rdlynx19/paper-byte/code/src/epub/Epub.cpp

#include <sys/types.h>
#include <sys/stat.h>
#include <unistd.h>
#ifndef UNIT_TEST
#include <esp_log.h>
#include <esp_system.h>
#include <freertos/FreeRTOS.h>
#include <freertos/task.h>
#else
#define ESP_LOGI(tag, args...) \
  printf(args);                \
  printf("\n");
#define ESP_LOGE(tag, args...) \
  printf(args);                \
  printf("\n");
#define ESP_LOGD(tag, args...) \
  printf(args);                \
  printf("\n");
#define ESP_LOGW(tag, args...) \
  printf(args);                \
  printf("\n");
#endif
#include <map>
#include "../vendor/tinyxml2.h"
#include "ZipFile.h"
#include "Epub.h"

static const char *TAG = "EPUB";

bool Epub::find_content_opf_file(ZipFile &zip, std::string &content_opf_file)
{
  // open up the meta data to find where the content.opf file lives
  char *meta_info = (char *)zip.read_file_to_memory("META-INF/container.xml");
  if (!meta_info)
  {
    ESP_LOGE(TAG, "Could not find META-INF/container.xml");
    return false;
  }
  // parse the meta data
  tinyxml2::XMLDocument meta_data_doc;
  auto result = meta_data_doc.Parse(meta_info);
  // finished with the data as it's been parsed
  free(meta_info);
  if (result != tinyxml2::XML_SUCCESS)
  {
    ESP_LOGE(TAG, "Could not parse META-INF/container.xml");
    return false;
  }
  auto container = meta_data_doc.FirstChildElement("container");
  if (!container)
  {
    ESP_LOGE(TAG, "Could not find container element in META-INF/container.xml");
    return false;
  }
  auto rootfiles = container->FirstChildElement("rootfiles");
  if (!rootfiles)
  {
    ESP_LOGE(TAG, "Could not find rootfiles element in META-INF/container.xml");
    return false;
  }
  // find the root file that has the media-type="application/oebps-package+xml"
  auto rootfile = rootfiles->FirstChildElement("rootfile");
  while (rootfile)
  {
    const char *media_type = rootfile->Attribute("media-type");
    if (media_type && strcmp(media_type, "application/oebps-package+xml") == 0)
    {
      const char *full_path = rootfile->Attribute("full-path");
      if (full_path)
      {
        content_opf_file = full_path;
        return true;
      }
    }
    rootfile = rootfile->NextSiblingElement("rootfile");
  }
  ESP_LOGE(TAG, "Could not get path to content.opf file");
  return false;
}

bool Epub::parse_content_opf(ZipFile &zip, std::string &content_opf_file)
{
  // read in the content.opf file and parse it
  char *contents = (char *)zip.read_file_to_memory(content_opf_file.c_str());
  // parse the contents
  tinyxml2::XMLDocument doc;
  auto result = doc.Parse(contents);
  free(contents);
  if (result != tinyxml2::XML_SUCCESS)
  {
    ESP_LOGE(TAG, "Error parsing content.opf - %s", doc.ErrorIDToName(result));
    return false;
  }
  auto package = doc.FirstChildElement("package");
  if (!package)
  {
    ESP_LOGE(TAG, "Could not find package element in content.opf");
    return false;
  }
  // get the metadata - title and cover image
  auto metadata = package->FirstChildElement("metadata");
  if (!metadata)
  {
    ESP_LOGE(TAG, "Missing metadata");
    return false;
  }
  auto title = metadata->FirstChildElement("dc:title");
  if (!title)
  {
    ESP_LOGE(TAG, "Missing title");
    return false;
  }
  m_title = title->GetText();

  auto creator = metadata->FirstChildElement("dc:creator");
  if (creator && creator->GetText())
    m_author = creator->GetText();
  else
    ESP_LOGW(TAG, "Missing author");

  auto cover = metadata->FirstChildElement("meta");
  while (cover && cover->Attribute("name") && strcmp(cover->Attribute("name"), "cover") != 0)
  {
    cover = cover->NextSiblingElement("meta");
  }
  if (!cover)
  {
    ESP_LOGW(TAG, "Missing cover");
  }
  auto cover_item = cover ? cover->Attribute("content") : nullptr;
  // read the manifest and spine
  // the manifest gives us the names of the files
  // the spine gives us the order of the files
  // we can then read the files in the order they are in the spine
  auto manifest = package->FirstChildElement("manifest");
  if (!manifest)
  {
    ESP_LOGE(TAG, "Missing manifest");
    return false;
  }
  // create a mapping from id to file name
  auto item = manifest->FirstChildElement("item");
  std::map<std::string, std::string> items;
  // EPUB3 fallback: <item properties="cover-image" .../>, used when there's
  // no EPUB2-style <meta name="cover"> (or its referenced id doesn't match
  // any manifest item).
  std::string epub3_cover_href;

  while (item)
  {
    const char *id_attr   = item->Attribute("id");
    const char *href_attr = item->Attribute("href");
    if (id_attr && href_attr) {
      std::string item_id = id_attr;
      std::string href    = m_base_path + href_attr;
      if (cover_item && item_id == cover_item)
        m_cover_image_item = href;
      if (item_id == "ncx")
        m_toc_ncx_item = href;
      const char *properties = item->Attribute("properties");
      if (properties && std::string(properties).find("cover-image") != std::string::npos)
        epub3_cover_href = href;
      items[item_id] = href;
    }
    item = item->NextSiblingElement("item");
  }
  if (m_cover_image_item.empty())
    m_cover_image_item = epub3_cover_href;
  // find the spine
  auto spine = package->FirstChildElement("spine");
  if (!spine)
  {
    ESP_LOGE(TAG, "Missing spine");
    return false;
  }
  // The spine's own toc="..." attribute is the authoritative reference to
  // the NCX manifest item — its id isn't required to be "ncx" (e.g. some
  // EPUB3 exports use id="toc" instead), so prefer it over the id=="ncx"
  // naming convention checked in the manifest loop above.
  const char *toc_id = spine->Attribute("toc");
  if (toc_id && items.find(toc_id) != items.end())
    m_toc_ncx_item = items[toc_id];
  // read the spine
  auto itemref = spine->FirstChildElement("itemref");
  while (itemref)
  {
    auto id = itemref->Attribute("idref");
    if (items.find(id) != items.end())
    {
      m_spine.push_back(std::make_pair(id, items[id]));
    }
    itemref = itemref->NextSiblingElement("itemref");
  }
  return true;
}

bool Epub::parse_toc_ncx_file(ZipFile &zip)
{
  // the ncx file should have been specified in the content.opf file
  if (m_toc_ncx_item.empty())
  {
    ESP_LOGE(TAG, "No ncx file specified");
    return false;
  }
  ESP_LOGI(TAG, "toc path: %s\n", m_toc_ncx_item.c_str());

  char *ncx_data = (char *)zip.read_file_to_memory(m_toc_ncx_item.c_str());
  if (!ncx_data)
  {
    ESP_LOGE(TAG, "Could not find %s", m_toc_ncx_item.c_str());
    return false;
  }
  // Parse the Toc contents
  tinyxml2::XMLDocument doc;
  auto result = doc.Parse(ncx_data);
  free(ncx_data);
  if (result != tinyxml2::XML_SUCCESS)
  {
    ESP_LOGE(TAG, "Error parsing toc %s", doc.ErrorIDToName(result));
    return false;
  }
  auto ncx = doc.FirstChildElement("ncx");
  if (!ncx)
  {
    ESP_LOGE(TAG, "Could not find first child ncx in toc");
    return false;
  }

  auto navMap = ncx->FirstChildElement("navMap");
  if (!navMap)
  {
    ESP_LOGE(TAG, "Could not find navMap child in ncx");
    return false;
  }

  parse_nav_points(navMap, 0);
  return true;
}

void Epub::parse_nav_points(tinyxml2::XMLElement *parent, int level)
{
  // Defensive cap on recursion depth — a real book's TOC is a handful of
  // levels deep at most; this just guards against a malformed or
  // pathologically nested NCX rather than reflecting any real limit.
  if (level > 8) return;

  auto navPoint = parent->FirstChildElement("navPoint");
  while (navPoint)
  {
    std::string title = "";
    auto navLabelEl = navPoint->FirstChildElement("navLabel");
    if (navLabelEl) {
      auto textEl = navLabelEl->FirstChildElement("text");
      if (textEl) {
        auto textNode = textEl->FirstChild();
        if (textNode) title = textNode->Value();
      }
    }

    auto content = navPoint->FirstChildElement("content");
    if (content) {
      const char *src = content->Attribute("src");
      if (src) {
        std::string href = m_base_path + src;
        std::string anchor = "";
        size_t pos = href.find('#');
        if (pos != std::string::npos) {
          anchor = href.substr(pos + 1);
          href   = href.substr(0, pos);
        }
        m_toc.push_back(EpubTocEntry(title, href, anchor, level));
      }
    }

    // Recurse before moving to the next sibling, so a parent's entry is
    // always immediately followed by all of its own descendants in m_toc
    // (depth-first, document order) before the next top-level entry.
    parse_nav_points(navPoint, level + 1);
    navPoint = navPoint->NextSiblingElement("navPoint");
  }
}

Epub::Epub(const std::string &path) : m_path(path)
{
}

// load in the meta data for the epub file
bool Epub::load()
{
  ZipFile zip(m_path.c_str());
  std::string content_opf_file;
  if (!find_content_opf_file(zip, content_opf_file))
  {
    #ifndef UNIT_TEST
      #ifdef USE_SPIFFS
        ESP_LOGI(TAG, "Is SPIFFs data uploaded?\npio run -t uploadfs");
      #endif
      ESP_LOGE(TAG, "Could not open ePub. Restarting in 10 secs.");
      vTaskDelay(pdMS_TO_TICKS(1000*10));
      esp_restart();
    #endif
    return false;
  }
  // get the base path for the content
  m_base_path = content_opf_file.substr(0, content_opf_file.find_last_of('/') + 1);
  if (!parse_content_opf(zip, content_opf_file))
  {
    return false;
  }
  if (!parse_toc_ncx_file(zip))
  {
    return false;
  }
  return true;
}

const std::string &Epub::get_title()
{
  return m_title;
}

const std::string &Epub::get_author()
{
  return m_author;
}

const std::string &Epub::get_cover_image_item()
{
  return m_cover_image_item;
}

std::string normalise_path(const std::string &path)
{
  std::vector<std::string> components;
  std::string component;
  for (auto c : path)
  {
    if (c == '/')
    {
      if (!component.empty())
      {
        if (component == "..")
        {
          if (!components.empty())
          {
            components.pop_back();
          }
        }
        else
        {
          components.push_back(component);
        }
        component.clear();
      }
    }
    else
    {
      component += c;
    }
  }
  if (!component.empty())
  {
    components.push_back(component);
  }
  std::string result;
  for (auto &component : components)
  {
    if (result.size() > 0)
    {
      result += "/";
    }
    result += component;
  }
  return result;
}

uint8_t *Epub::get_item_contents(const std::string &item_href, size_t *size)
{
  ZipFile zip(m_path.c_str());
  std::string path = normalise_path(item_href);
  auto content = zip.read_file_to_memory(path.c_str(), size);
  if (!content)
  {
    ESP_LOGE(TAG, "Failed to read item %s", path.c_str());
    return nullptr;
  }
  return content;
}

int Epub::get_spine_items_count()
{
  return m_spine.size();
}

std::string &Epub::get_spine_item(int spine_index)
{
  if (spine_index < 0 || spine_index >= (int)m_spine.size()) {
    ESP_LOGI(TAG, "get_spine_item index:%d is out of range", spine_index);
    spine_index = 0;
  }
  return m_spine[spine_index].second;
}

EpubTocEntry &Epub::get_toc_item(int toc_index)
{
  return m_toc[toc_index];
}

int Epub::get_toc_items_count()
{
  return m_toc.size();
}

// work out the section index for a toc index
int Epub::get_spine_index_for_toc_index(int toc_index)
{
  // the toc entry should have an href that matches the spine item
  // so we can find the spine index by looking for the href
  for (int i = 0; i < m_spine.size(); i++)
  {
    if (m_spine[i].second == m_toc[toc_index].href)
    {
      return i;
    }
  }
  ESP_LOGI(TAG, "Section not found");
  // not found - default to the start of the book
  return 0;
}

// work out which toc entry covers a given spine index
int Epub::get_toc_index_for_spine_index(int spine_index)
{
  int best       = -1;
  int best_spine = -1;
  for (int i = 0; i < (int)m_toc.size(); i++)
  {
    int s = get_spine_index_for_toc_index(i);
    if (s <= spine_index && s > best_spine)
    {
      best       = i;
      best_spine = s;
    }
  }
  return best;
}
